KeremKoksal/KLOR-Handmade/case/Alternate Case Design/Tenting Legs/images/TentingLeg38mm.png

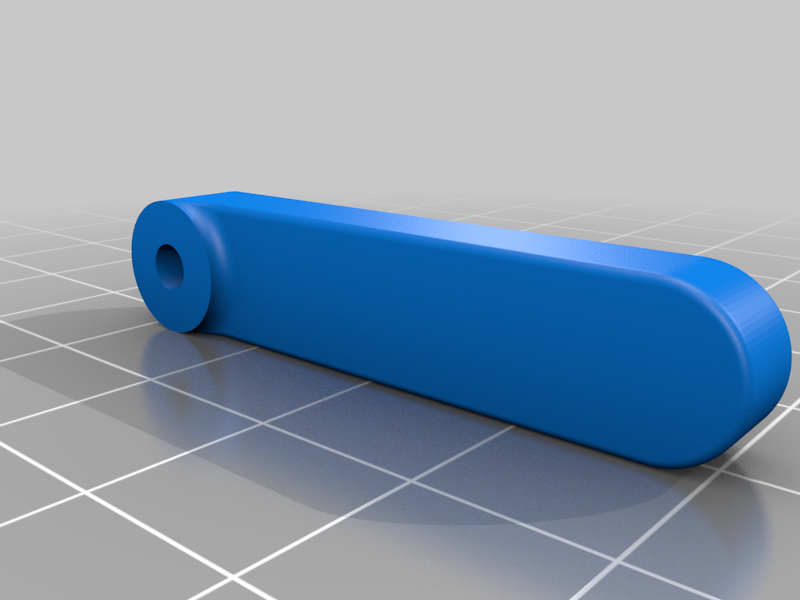
case/Alternate Case Design/Tenting Legs/images/TentingLeg38mm.png
