KeremKoksal/KLOR-Handmade/docs/images/Klor_1.4_picture8.png

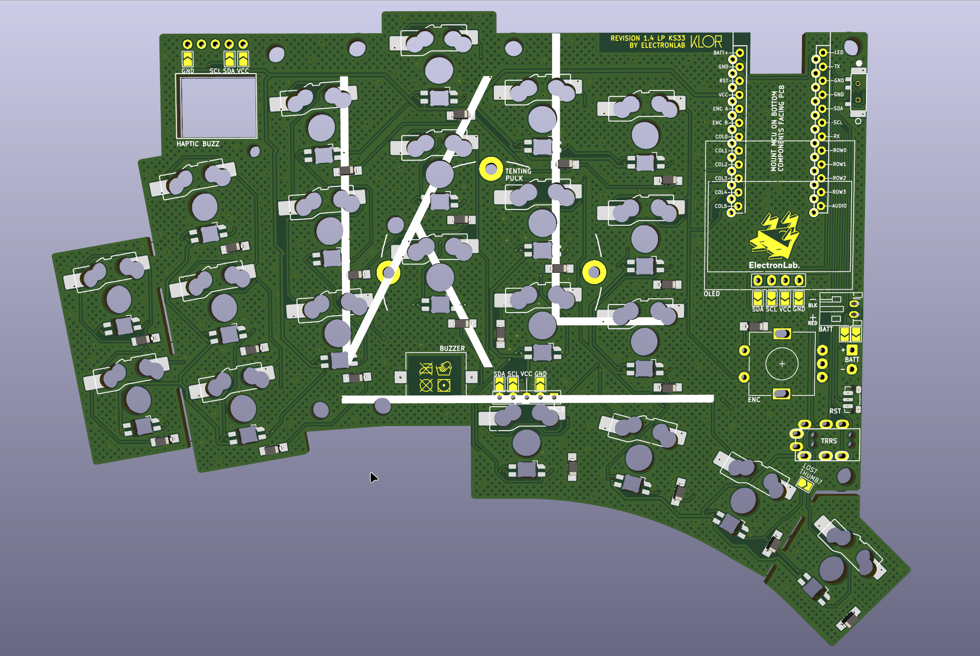
docs/images/Klor_1.4_picture8.png
