KeremKoksal/KLOR-Handmade/docs/images/Klor_1.4_picture10.png

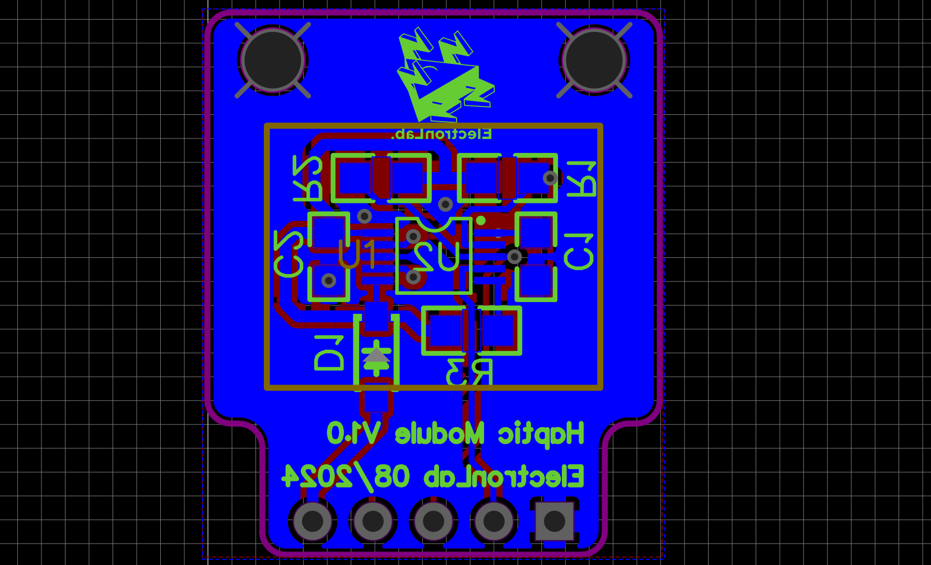
docs/images/Klor_1.4_picture10.png
