KeremKoksal/KLOR-Handmade/docs/images/Klor_1.4_picture11.png

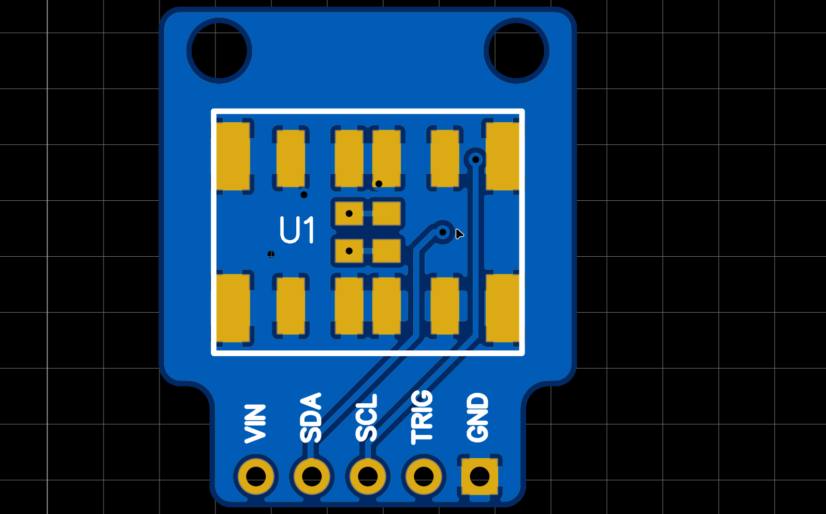
docs/images/Klor_1.4_picture11.png
