KeremKoksal/KLOR-Handmade/docs/images/Klor_1.4_picture12.png

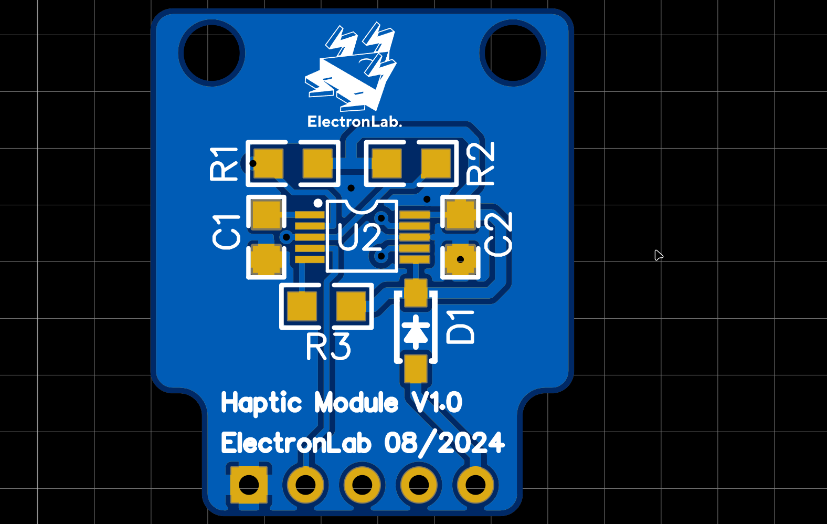
docs/images/Klor_1.4_picture12.png
