KeremKoksal/KLOR-Handmade/docs/images/KLOR_1.5.png

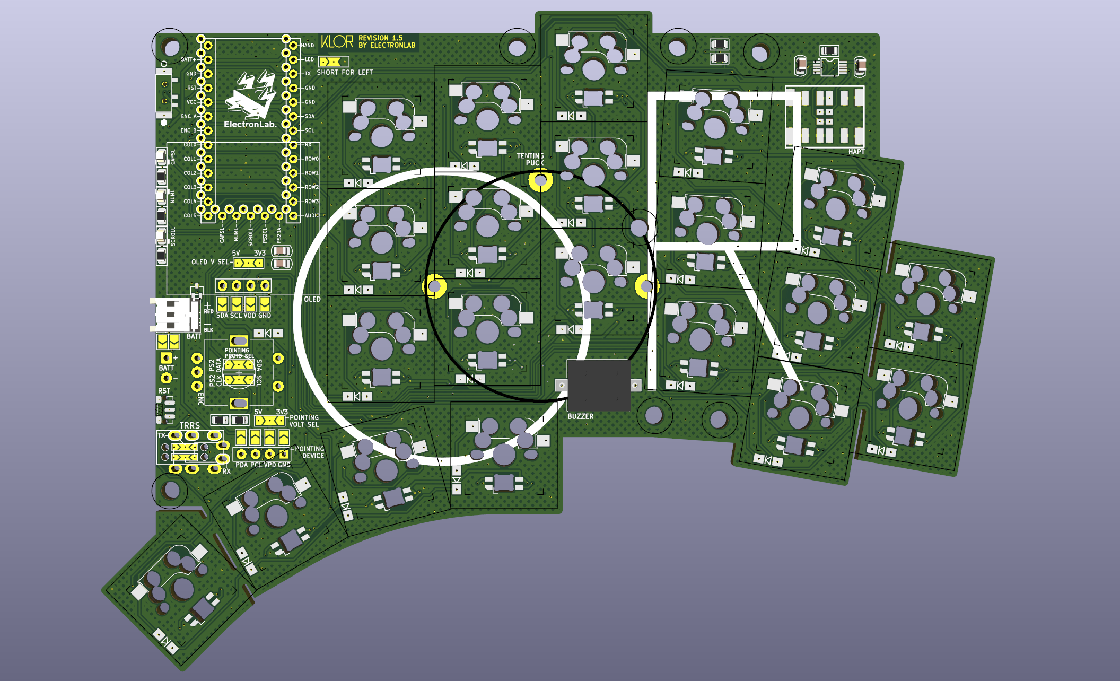
docs/images/KLOR_1.5.png
