KeremKoksal/KLOR-Handmade/docs/images/KLOR_1.5_picture1.png

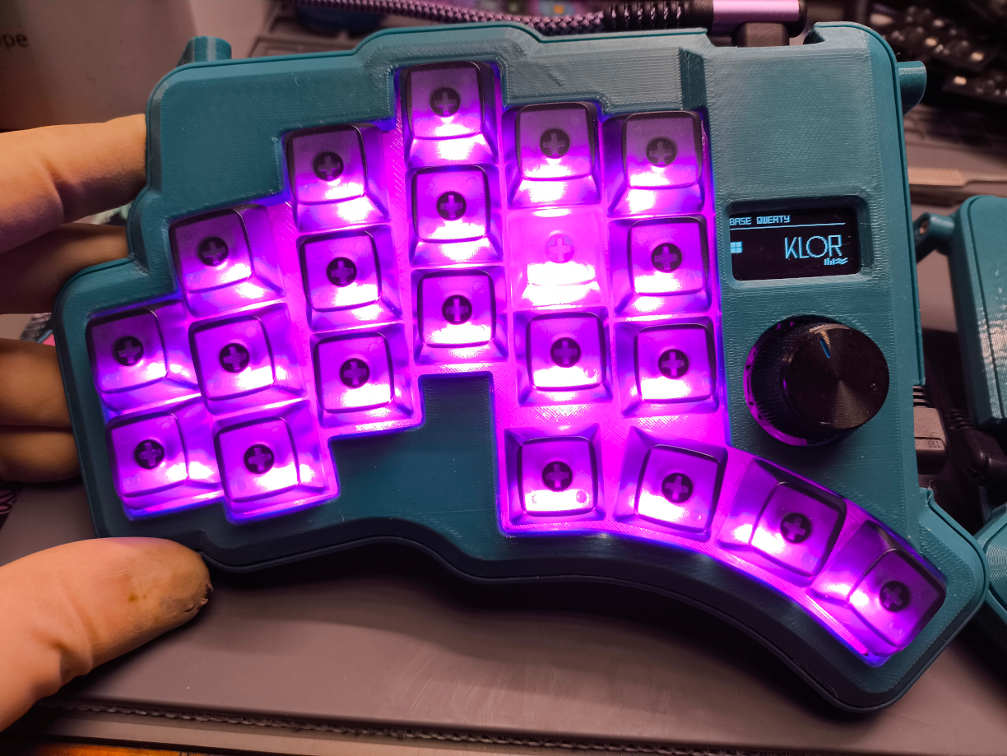
docs/images/KLOR_1.5_picture1.png
