KeremKoksal/KLOR-Handmade/docs/images/KLOR_1.5_picture2.png

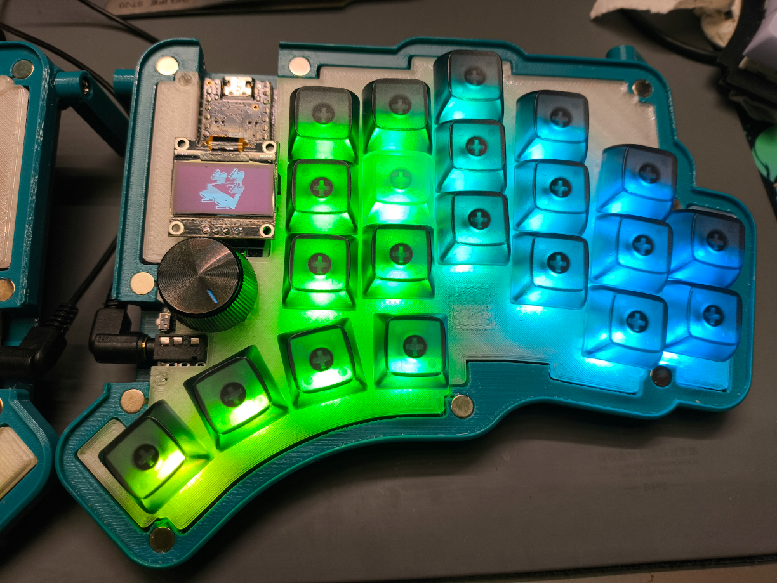
docs/images/KLOR_1.5_picture2.png
