KeremKoksal/KLOR-Handmade/docs/images/KLOR_1.5_picture3.png

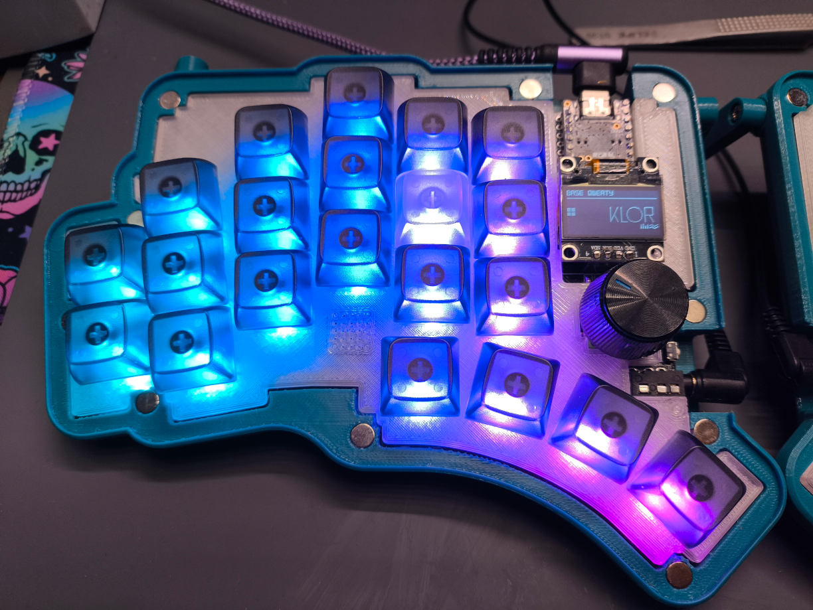
docs/images/KLOR_1.5_picture3.png
