KeremKoksal/KLOR-Handmade/docs/images/KLOR_1.5_picture4.png

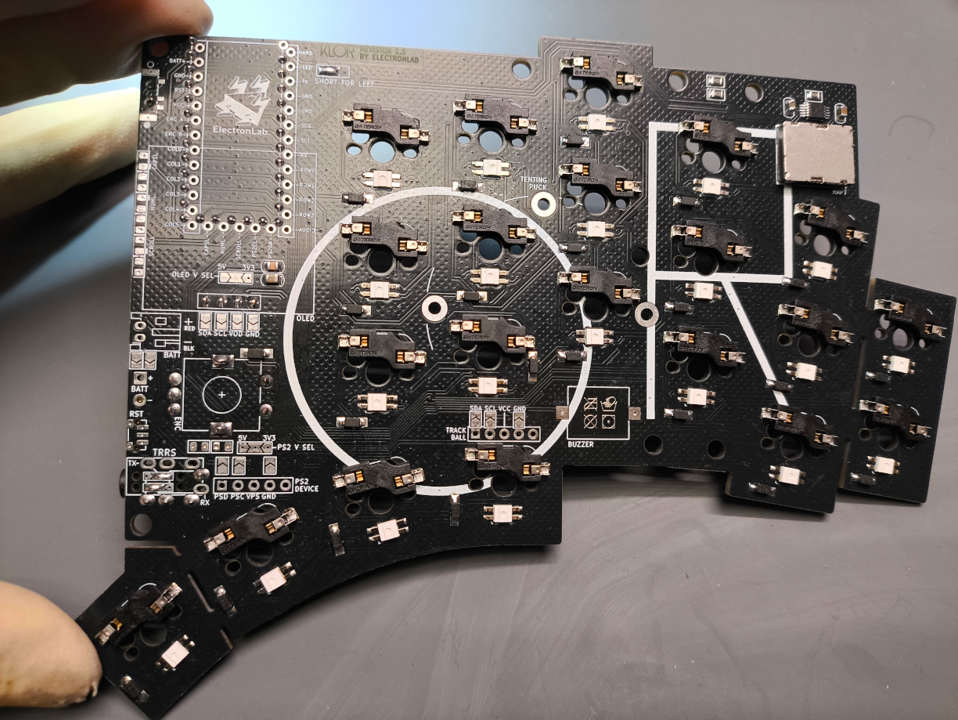
docs/images/KLOR_1.5_picture4.png
