KeremKoksal/KLOR-Handmade/docs/images/KLOR_1.5_picture5.png

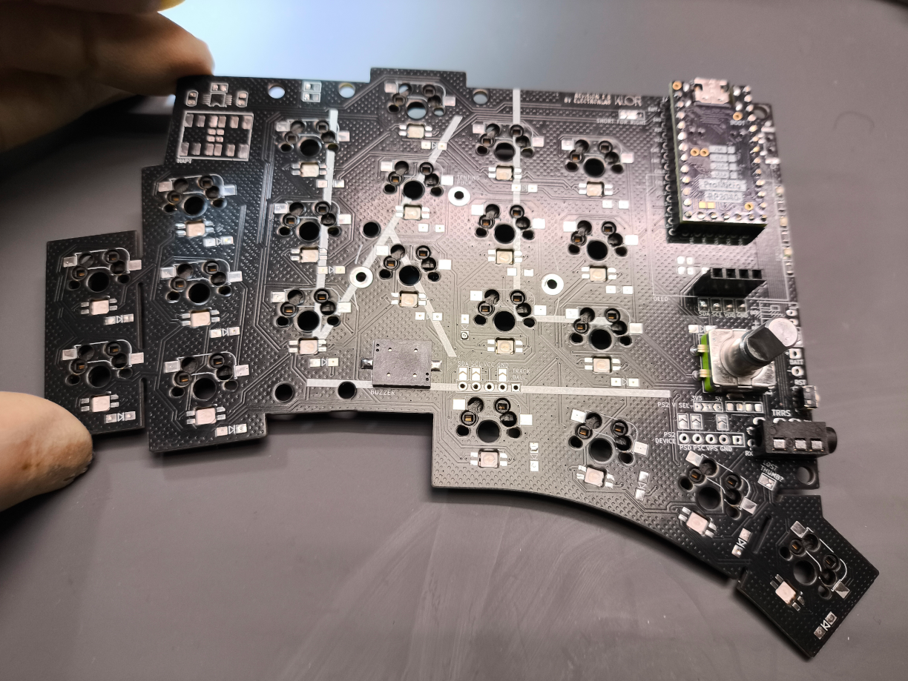
docs/images/KLOR_1.5_picture5.png
