KeremKoksal/KLOR-Handmade/case/Alternate Case Design/Tenting Legs/files/tentingleg36mm.stl

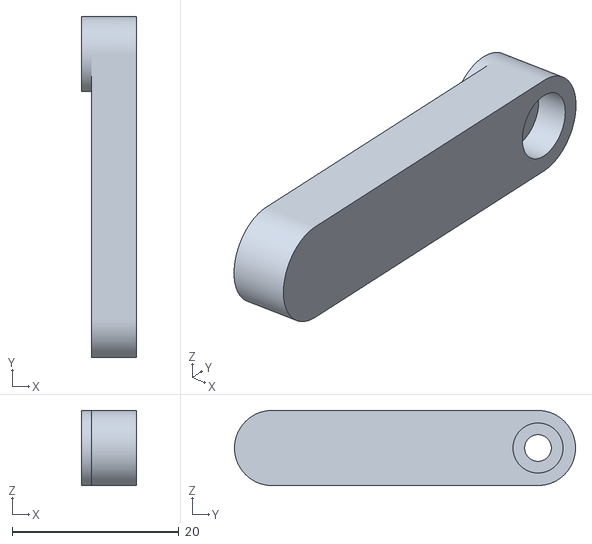
[picture p43: CAD file, 2024-08-09]
case/Alternate Case Design/Tenting Legs/files/tentingleg36mm.stl
6.60 x 40.9 x 9.00
