KeremKoksal/KLOR-Handmade/case/Alternate Case Design/Yubitsume/v1-Lid-Yubitsume-noOLED.stl

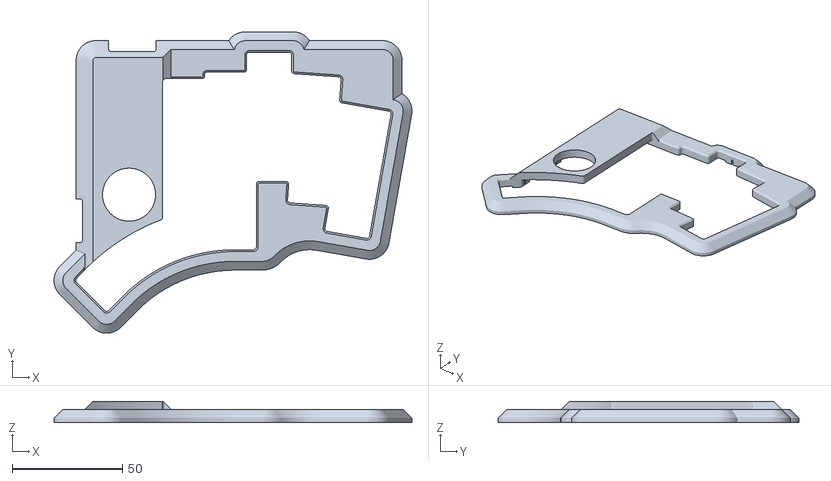
[picture p44: CAD file, 2024-07-25]
case/Alternate Case Design/Yubitsume/v1-Lid-Yubitsume-noOLED.stl
162.2 x 136.5 x 9.60
