KeremKoksal/KLOR-Handmade/case/Alternate Case Design/Yubitsume/v1-Base-Yubitmsume.stl

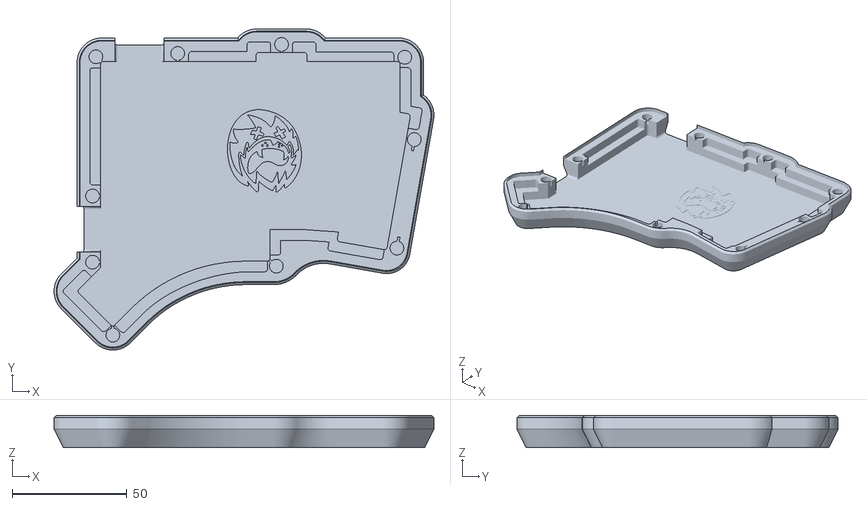
[picture p48: CAD file, 2024-07-25]
case/Alternate Case Design/Yubitsume/v1-Base-Yubitmsume.stl
165.8 x 140.1 x 14.0
