KeremKoksal/KLOR-Handmade/case/Alternate Case Design/Tenting Legs/files/tentingLeg40mm.stl

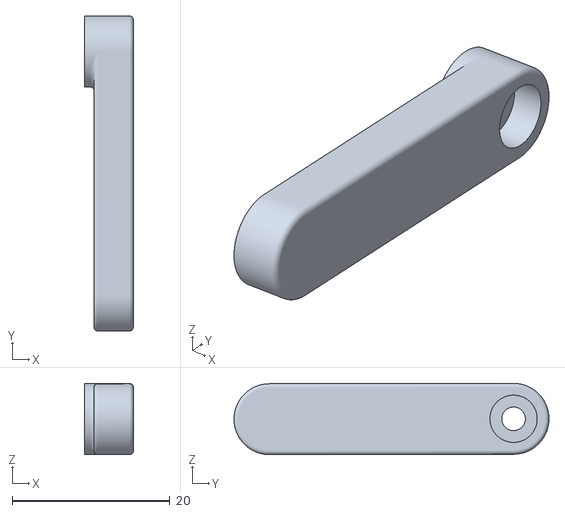
[picture p49: CAD file, 2024-08-09]
case/Alternate Case Design/Tenting Legs/files/tentingLeg40mm.stl
6.21 x 40.0 x 9.06
